squaresolid/benjolin_gorga/benjolin3dpics/benjolin_1.6_back_side_full.png

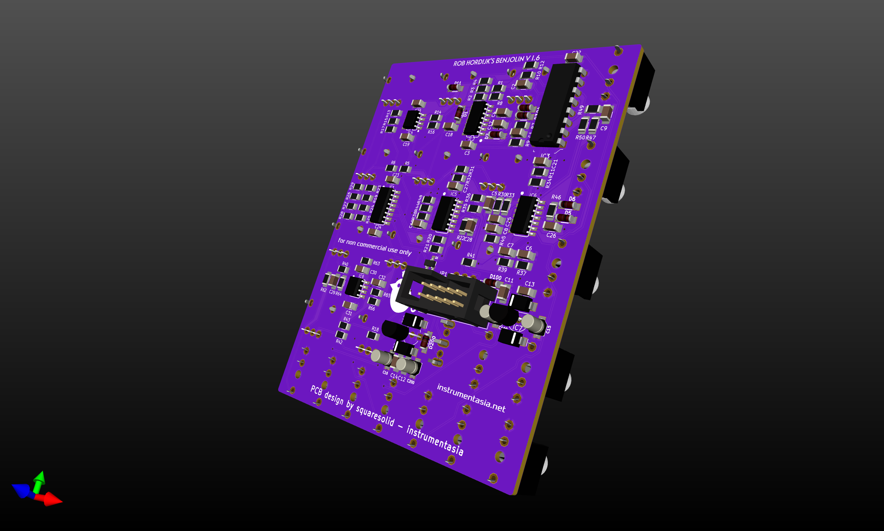
benjolin3dpics/benjolin_1.6_back_side_full.png
