squaresolid/benjolin_gorga/benjolin3dpics/benjolin_1.6_back_wire_side2.png

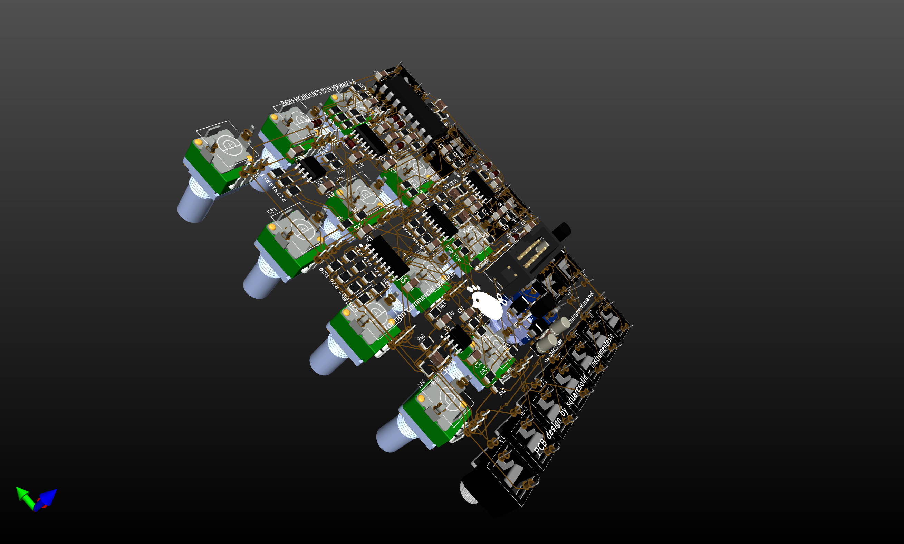
benjolin3dpics/benjolin_1.6_back_wire_side2.png
