squaresolid/benjolin_gorga/benjolin3dpics/benjolin_1.6_back_wire_side.png

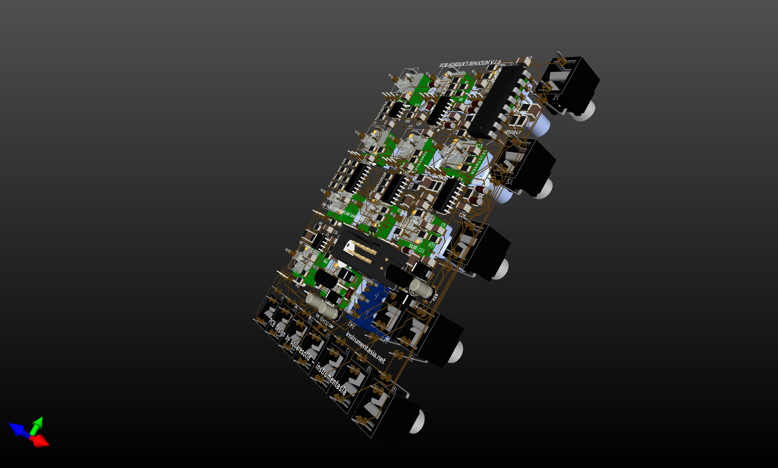
benjolin3dpics/benjolin_1.6_back_wire_side.png
