squaresolid/benjolin_gorga/benjolin_1.6_2.kicad_sch

## KiCad design benjolin_1.6_2.kicad_sch (2022-10-09)

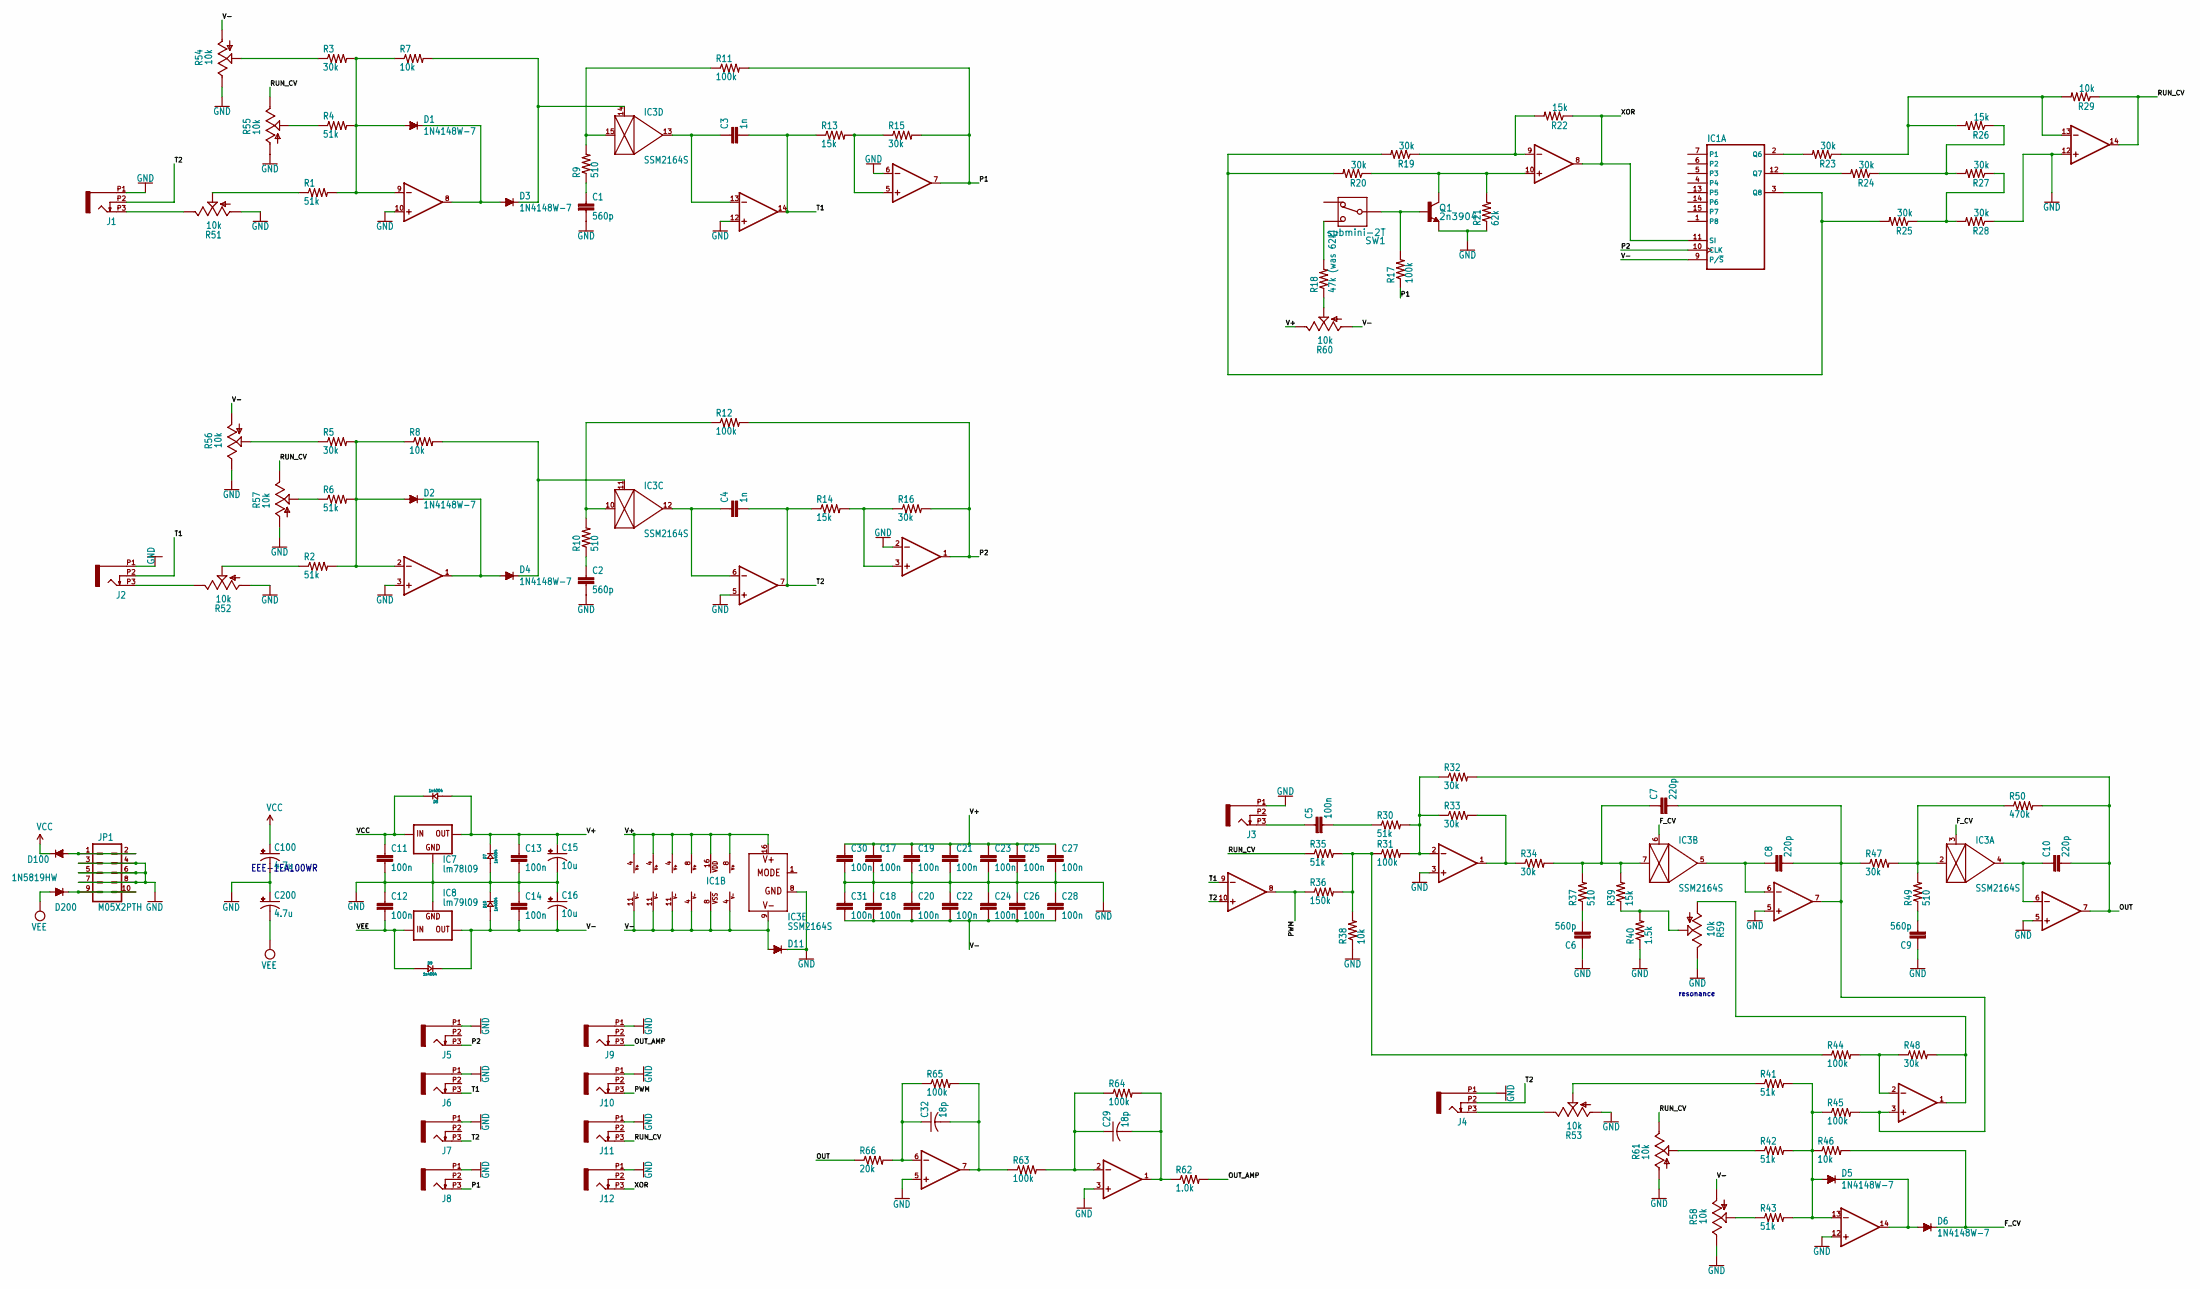
[picture p23: schematic benjolin_1.6_2.kicad_sch]

Parts:
C1, C2, C6, C9: 560p; C_1206_3216Metric_Pad1.33x1.80mm_HandSolder
C3, C4: 1n; C_1206_3216Metric_Pad1.33x1.80mm_HandSolder
C5, C11, C12, C13, C14, C17, C18, C19, C20, C21, C22, C23, C24, C25, C26, C27, C28, C30, C31: 100n; C_1206_3216Metric_Pad1.33x1.80mm_HandSolder
C7, C8, C10: 220p; C_1206_3216Metric_Pad1.33x1.80mm_HandSolder
C15, C16: 10u; PANASONIC_A
C29, C32: 18p; C_1206_3216Metric_Pad1.33x1.80mm_HandSolder
C100, C200: 4.7u; PANASONIC_A
D1, D2, D3, D4, D5, D6: 1N4148W-7; SOD123
D7, D8, D9, D10: 1n4004; DO-214AC
D11, D100, D200: 1N5819HW; SOD123
IC1: 4021D; SO16
IC2, IC5, IC6: TL074D; SO14
IC3: SSM2164S; DIP-16_W7.62mm
IC4, IC9: TL072D; SO08
IC7: lm78l09; TO-92L_Inline_Wide_Vreg78L09
IC8: lm79l09; TO-92L_Inline_Wide_Vreg79L09
J1, J2, J3, J4, J5, J6, J7, J8, J9, J10, J11, J12: PJ301_THONKICONN6; WQP_PJ_301M6
JP1: M05X2PTH; IDC-Header_2x05_P2.54mm_Vertical
Q1: 2n3904; SOT23-3
R1, R2, R4, R6, R30, R35, R41, R42, R43: 51k; R_1206_3216Metric_Pad1.30x1.75mm_HandSolder
R3, R5, R15, R16, R19, R20, R23, R24, R25, R27, R28, R32, R33, R34, R47, R48: 30k; R_1206_3216Metric_Pad1.30x1.75mm_HandSolder
R7, R8, R29, R38, R46: 10k; R_1206_3216Metric_Pad1.30x1.75mm_HandSolder
R9, R10, R37, R49: 510; R_1206_3216Metric_Pad1.30x1.75mm_HandSolder
R11, R12, R17, R31, R44, R45, R63, R64, R65: 100k; R_1206_3216Metric_Pad1.30x1.75mm_HandSolder
R13, R14, R22, R26, R39: 15k; R_1206_3216Metric_Pad1.30x1.75mm_HandSolder
R18: 47k (was 62k); R_1206_3216Metric_Pad1.30x1.75mm_HandSolder
R21: 62k; R_1206_3216Metric_Pad1.30x1.75mm_HandSolder
R36: 150k; R_1206_3216Metric_Pad1.30x1.75mm_HandSolder
R40: 1.5k; R_1206_3216Metric_Pad1.30x1.75mm_HandSolder
R50: 470k; R_1206_3216Metric_Pad1.30x1.75mm_HandSolder
R51, R52, R53, R54, R55, R56, R57, R58, R59, R60, R61: 10k; ALPS_POT_VERTICAL_PS
R62: 1.0k; R_1206_3216Metric_Pad1.30x1.75mm_HandSolder
R66: 20k; R_1206_3216Metric_Pad1.30x1.75mm_HandSolder
SW1: submini-2T; SPDT-SUB

Connections:
F_CV: D6.C, IC3.3 (CTRL), IC3.6 (CTRL), R46.2
GND: C1.2, C2.2, C6.1, C9.1, C11.2, C12.1, C13.2, C14.1, C15.-, C16.+, C17.2, C18.1, C19.2, C20.1, C21.2, C22.1, C23.2, C24.1, C25.2, C26.1, C27.2, C28.1, C30.2, C31.1, C100.-, C200.+, D7.1 (+), D10.2 (-), D11.C, IC2.3 (+IN), IC2.5 (+IN), IC2.10 (+IN), IC2.12 (+IN), IC3.8 (GND), IC4.2 (-IN), IC4.6 (-IN), IC5.5 (+IN), IC5.12 (+IN), IC6.3 (+IN), IC6.5 (+IN), IC6.12 (+IN), IC7.GND, IC8.GND, IC9.3 (+IN), IC9.5 (+IN), J1.P1 (1), J2.P1 (1), J3.P1 (1), J4.P1 (1), J5.P1 (1), J6.P1 (1), J7.P1 (1), J8.P1 (1), J9.P1 (1), J10.P1 (1), J11.P1 (1), J12.P1 (1), JP1.3, JP1.4, JP1.5, JP1.6, JP1.7, JP1.8, Q1.2 (E), R21.1, R28.1, R38.1, R40.1, R51.P$3 (A), R52.P$3 (A), R53.P$3 (A), R54.P$1 (E), R55.P$3 (A), R56.P$1 (E), R57.P$3 (A), R58.P$1 (E), R59.P$1 (E), R61.P$3 (A)
unnamed: C1.1, R9.1
unnamed: C2.1, R10.1
unnamed: C3.1, IC2.13 (-IN), IC3.13 (OUT)
unnamed: C4.1, IC2.6 (-IN), IC3.12 (OUT)
unnamed: C5.1, J3.P3 (3)
unnamed: C5.2, R30.1
unnamed: C6.2, R37.1
unnamed: C7.1, IC3.7 (IN), R34.2, R37.2, R39.2
unnamed: C7.2, C8.2, IC5.3 (+IN), IC6.7 (OUT), R45.2, R47.1
unnamed: C8.1, IC3.5 (OUT), IC6.6 (-IN)
unnamed: C9.2, R49.1
unnamed: C10.1, IC3.4 (OUT), IC5.6 (-IN)
unnamed: C29.1, IC9.2 (-IN), R63.2, R64.1
unnamed: C29.2, IC9.1 (OUT), R62.1, R64.2
unnamed: C32.1, IC9.6 (-IN), R65.1, R66.2
unnamed: C32.2, IC9.7 (OUT), R63.1, R65.2
unnamed: D1.A, IC2.9 (-IN), R1.2, R3.2, R4.2, R7.1
unnamed: D1.C, D3.A, IC2.8 (OUT)
unnamed: D2.A, IC2.2 (-IN), R2.2, R5.2, R6.2, R8.1
unnamed: D2.C, D4.A, IC2.1 (OUT)
unnamed: D3.C, IC3.14 (CTRL), R7.2
unnamed: D4.C, IC3.11 (CTRL), R8.2
unnamed: D5.A, IC6.13 (-IN), R41.2, R42.2, R43.2, R45.1, R46.1
unnamed: D5.C, D6.A, IC6.14 (OUT)
unnamed: D100.A, JP1.1, JP1.2
unnamed: D200.C, JP1.9, JP1.10
unnamed: IC1.2 (Q6), R23.2
unnamed: IC1.3 (Q8), R19.2, R20.2, R25.2
unnamed: IC1.12 (Q7), R24.2
unnamed: IC3.2 (IN), R47.2, R49.2, R50.1
unnamed: IC3.10 (IN), R10.2, R12.1
unnamed: IC3.15 (IN), R9.2, R11.1
unnamed: IC4.3 (+IN), R14.2, R16.1
unnamed: IC4.5 (+IN), R13.2, R15.1
unnamed: IC5.1 (OUT), R48.2, R59.P$3 (A)
unnamed: IC5.2 (-IN), R44.2, R48.1
unnamed: IC5.9 (-IN), R19.1, R22.2
unnamed: IC5.10 (+IN), Q1.3 (C), R20.1, R21.2
unnamed: IC5.13 (-IN), R23.1, R26.2, R29.2
unnamed: IC6.1 (OUT), R33.2, R34.1
unnamed: IC6.2 (-IN), R30.2, R31.2, R32.1, R33.1
unnamed: J1.P3 (3), R51.P$1 (E)
unnamed: J2.P3 (3), R52.P$1 (E)
unnamed: J4.P3 (3), R53.P$1 (E)
unnamed: Q1.1 (B), R17.2, SW1.P$2
unnamed: R1.1, R51.P$2 (S)
unnamed: R2.1, R52.P$2 (S)
unnamed: R3.1, R54.P$2 (S)
unnamed: R4.1, R55.P$2 (S)
unnamed: R5.1, R56.P$2 (S)
unnamed: R18.1, R60.P$2 (S)
unnamed: R18.2, SW1.P$1
unnamed: R24.1, R26.1, R27.2
unnamed: R25.1, R27.1, R28.2
unnamed: R31.1, R35.2, R36.2, R38.2, R44.1
unnamed: R39.1, R40.2, R59.P$2 (S)
unnamed: R41.1, R53.P$2 (S)
unnamed: R42.1, R61.P$2 (S)
unnamed: R43.1, R58.P$2 (S)
unnamed: R6.1, R57.P$2 (S)
OUT: C10.2, IC5.7 (OUT), R32.2, R50.2, R66.1
OUT_AMP: J9.P3 (3), R62.2
P1: IC4.7 (OUT), J8.P3 (3), R11.2, R15.2, R17.1
P2: IC1.10 (CLK), IC4.1 (OUT), J5.P3 (3), R12.2, R16.2
PWM: IC6.8 (OUT), J10.P3 (3), R36.1
RUN_CV: IC5.14 (OUT), J11.P3 (3), R29.1, R35.1, R55.P$1 (E), R57.P$1 (E), R61.P$1 (E)
T1: C3.2, IC2.14 (OUT), IC6.9 (-IN), J2.P2 (2), J6.P3 (3), R13.1
T2: C4.2, IC2.7 (OUT), IC6.10 (+IN), J1.P2 (2), J4.P2 (2), J7.P3 (3), R14.1
V+: C13.1, C15.+, C17.1, C19.1, C21.1, C23.1, C25.1, C27.1, C30.1, D7.2 (-), D8.1 (+), IC1.16 (VDD), IC2.4 (V+), IC3.16 (V+), IC4.8 (V+), IC5.4 (V+), IC6.4 (V+), IC7.OUT, IC9.8 (V+), R60.P$1 (E)
V-: C14.2, C16.-, C18.2, C20.2, C22.2, C24.2, C26.2, C28.2, C31.2, D9.2 (-), D10.1 (+), D11.A, IC1.8 (VSS), IC1.9 (P/~S), IC2.11 (V-), IC3.9 (V-), IC4.4 (V-), IC5.11 (V-), IC6.11 (V-), IC8.OUT, IC9.4 (V-), R54.P$3 (A), R56.P$3 (A), R58.P$3 (A), R60.P$3 (A)
VCC: C11.1, C100.+, D8.2 (-), D100.C, IC7.IN
VEE: C12.2, C200.-, D9.1 (+), D200.A, IC8.IN
XOR: IC1.11 (SI), IC5.8 (OUT), J12.P3 (3), R22.1

Notes on the sheet:
resonance
EEE-1EA100WR
